mend0z0/HotPlate/Hardware/v1_20230725/Design Folder/_HW_HotPlate/Output files/3D View/_3DView_Top_HotPlate_v1.0 - Copy.png

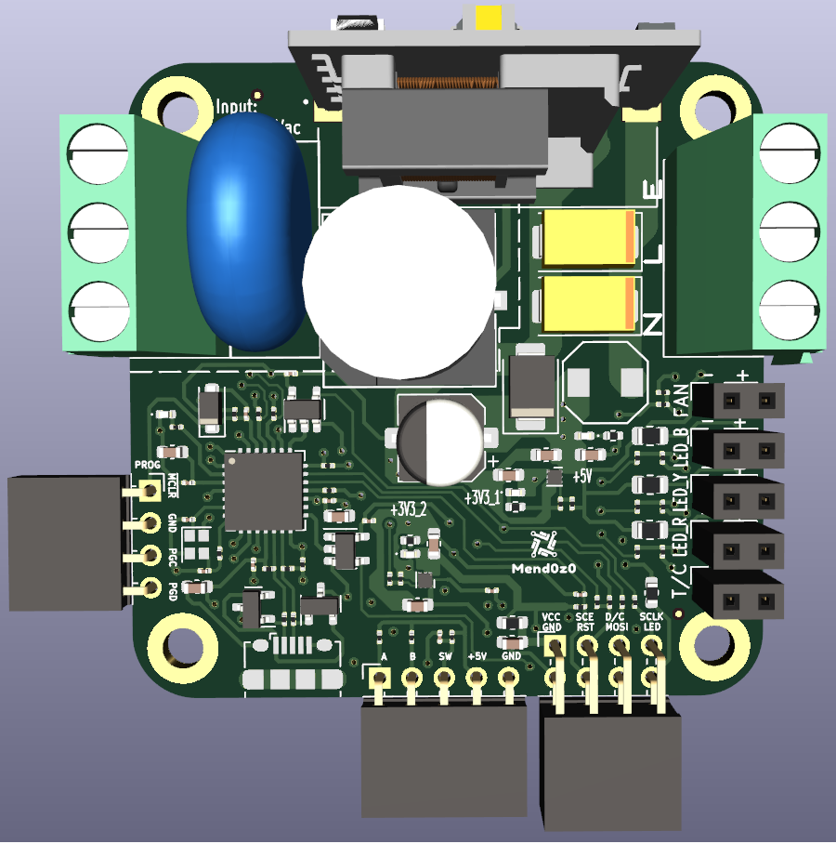
Hardware/v1_20230725/Design Folder/_HW_HotPlate/Output files/3D View/_3DView_Top_HotPlate_v1.0 - Copy.png
